wasalm/LoRaWAN-P2P-Tally-light/firmware-light/src/encryption.h

//
//  crypto.h
//  lorawan
//
//  Copied from https://github.com/things4u/ESP-1ch-Gateway
//

#ifndef ENCRYPTION_H
#define ENCRYPTION_H

#include <stdint.h>
void AES_Encrypt(uint8_t* data, uint8_t* key);
void AES_Decrypt(uint8_t* data, uint8_t* key);
uint8_t encodePacket(uint8_t *Data, uint8_t DataLength, uint32_t FrameCount, uint8_t *DevAddr, uint8_t *AppSKey, uint8_t Direction);
void AES_CMAC(uint8_t *data, uint8_t len, uint8_t *result, uint8_t * AppKey);

#else
#error "ENCRYPTION_H not defined"
#endif

//MIT License
//
//Copyright (c) 2016-2021 M. Westenberg / Things4U
//
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
